sebastian-stumpf/abomination/pcb/sepp/models/xiao_rp2040.step

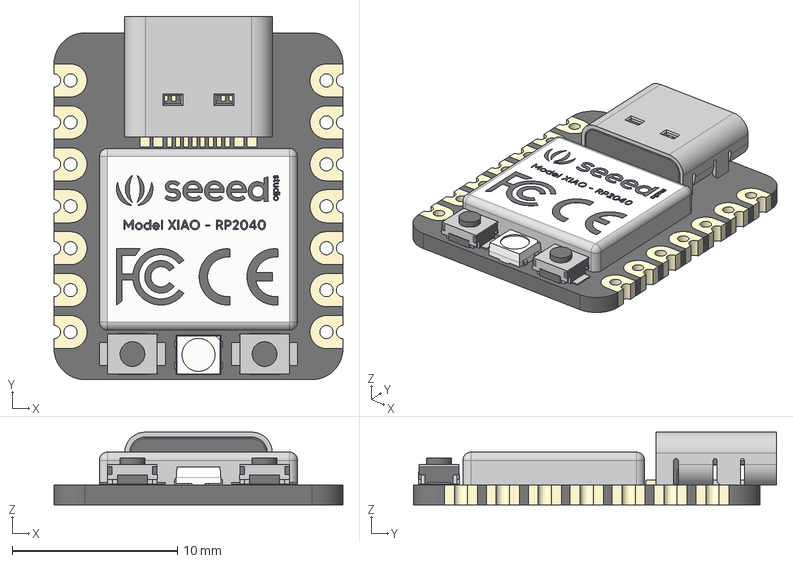
[picture p17: CAD file, 2023-10-14]
pcb/sepp/models/xiao_rp2040.step
17.5 x 22.0 x 4.40 mm
type-c v2
smd_button v3
DOUT
DIN
VSS
VDD
smd_button v3(Mirror)
