sebastian-stumpf/abomination/pcb/sepp/models/Liatris.step

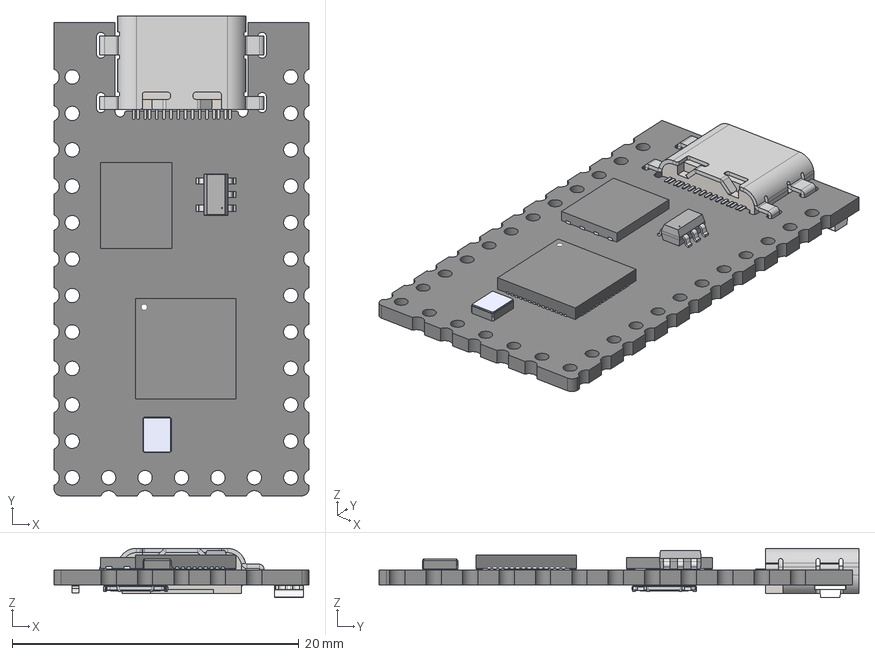
[picture p18: CAD file, 2023-10-14]
pcb/sepp/models/Liatris.step
17.8 x 33.5 x 3.44 mm
RP2040 PCB
