sebastian-stumpf/abomination/pcb/sepp/models/MBK-1u.step

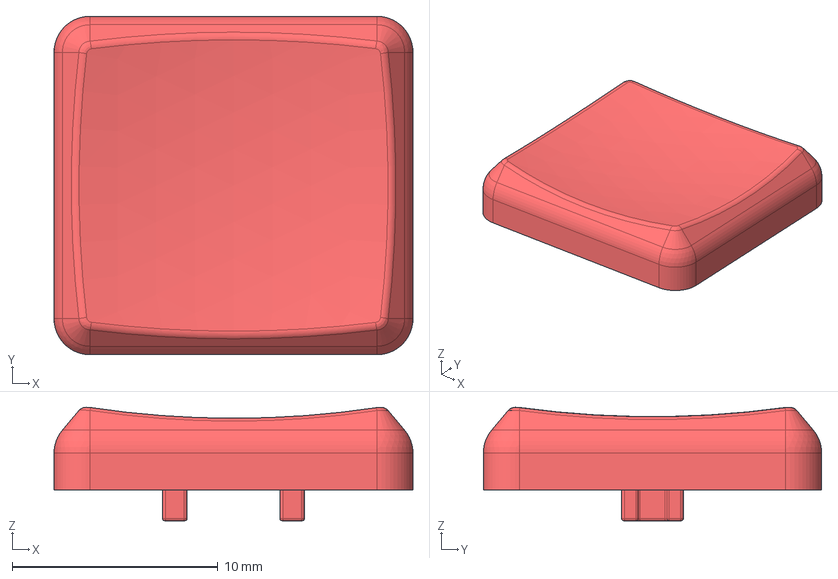
[picture p19: CAD file, 2023-10-14]
pcb/sepp/models/MBK-1u.step
17.4 x 16.4 x 5.52 mm
