sebastian-stumpf/abomination/pcb/sepp/models/pg1350-mbk.step

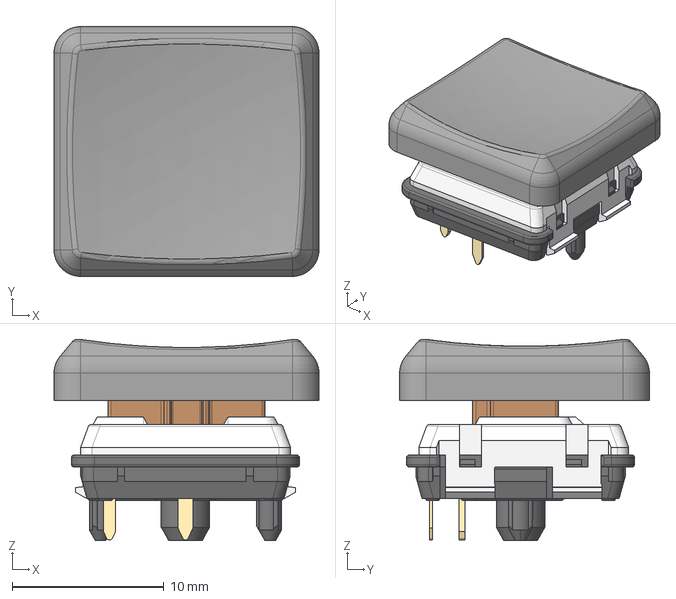
[picture p21: CAD file, 2023-10-14]
pcb/sepp/models/pg1350-mbk.step
17.4 x 16.4 x 13.3 mm
(Unsaved)
Document x 5
