sebastian-stumpf/abomination/pcb/sepp/models/EC12E-085.step

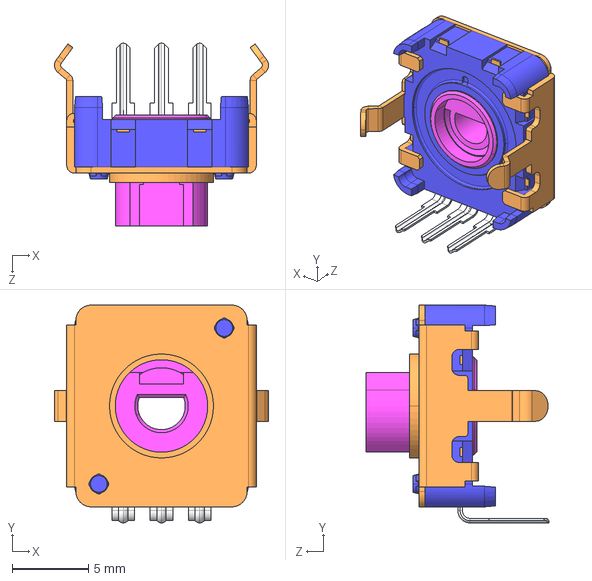
[picture p22: CAD file, 2023-10-14]
pcb/sepp/models/EC12E-085.step
14.0 x 14.3 x 11.9 mm
