sebastian-stumpf/abomination/pcb/sepp/models/SKRTLAE010.step

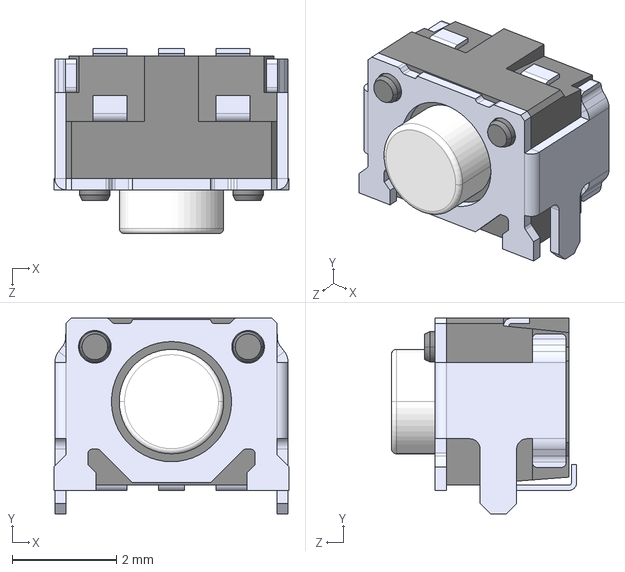
[picture p23: CAD file, 2023-10-14]
pcb/sepp/models/SKRTLAE010.step
4.50 x 3.75 x 3.55 mm
