sebastian-stumpf/abomination/pcb/sepp/models/SW_SKHLLC.step

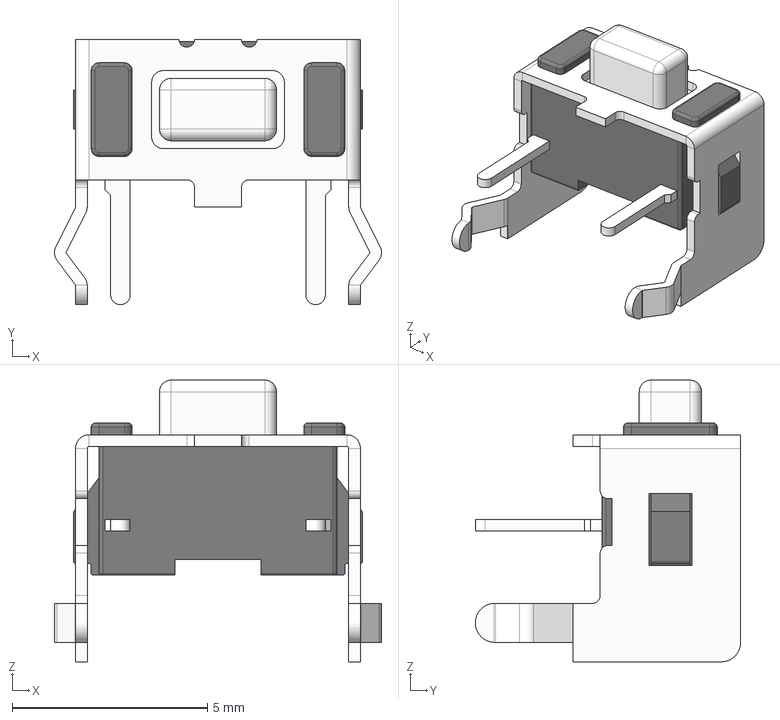
[picture p24: CAD file, 2023-10-14]
pcb/sepp/models/SW_SKHLLC.step
8.38 x 6.80 x 7.22 mm
