sebastian-stumpf/abomination/pcb/sepp/models/EC11-THT-15F-black.step

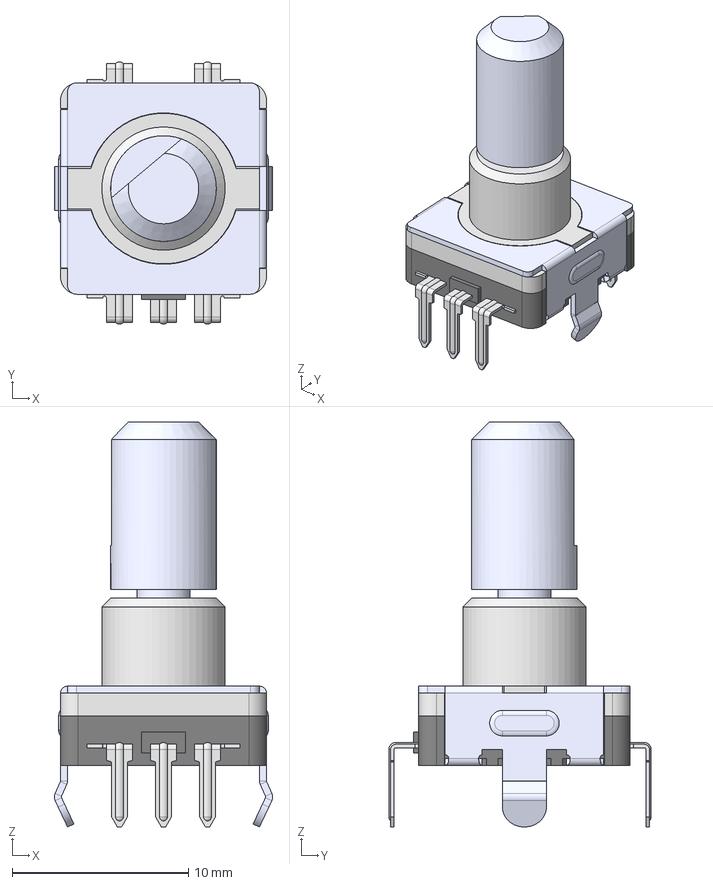
[picture p25: CAD file, 2023-10-14]
pcb/sepp/models/EC11-THT-15F-black.step
12.4 x 14.9 x 23.0 mm
Lb5
15F
EC11-Housing-THT
