sebastian-stumpf/abomination/pcb/sepp/models/LED_SK6812MINI-E.step

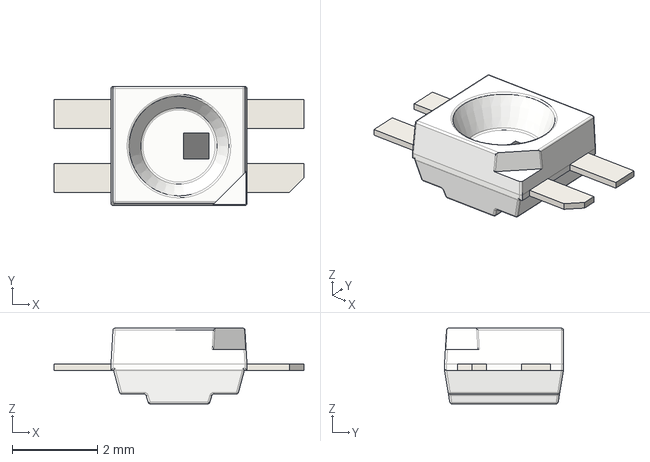
[picture p26: CAD file, 2023-10-14]
pcb/sepp/models/LED_SK6812MINI-E.step
5.88 x 2.80 x 1.78 mm
