sebastian-stumpf/abomination/pcb/sepp/models/SW_PUSH_6mm.step

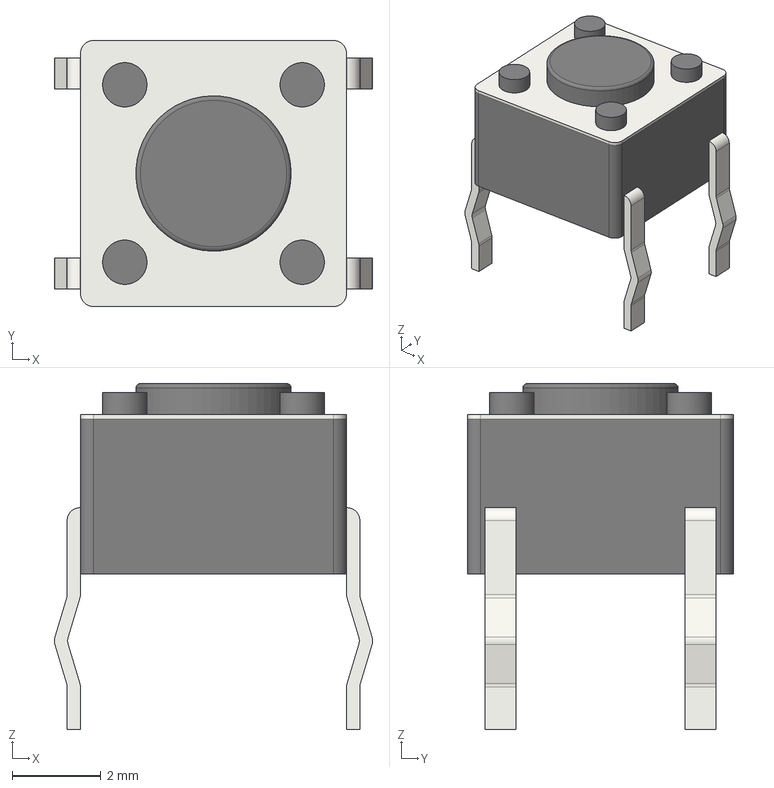
[picture p27: CAD file, 2023-10-14]
pcb/sepp/models/SW_PUSH_6mm.step
7.17 x 6.00 x 7.80 mm
