sebastian-stumpf/abomination/pcb/sepp/models/cherry mx.STEP

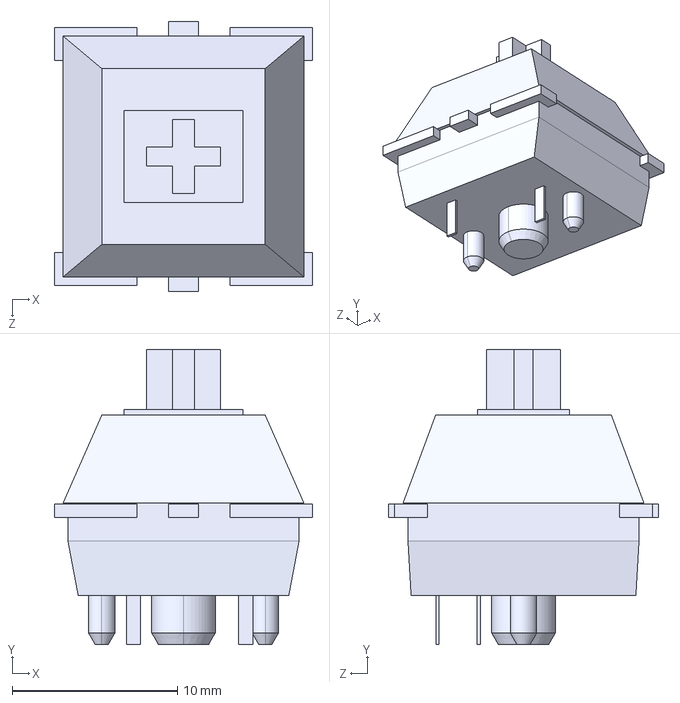
[picture p28: CAD file, 2023-10-14]
pcb/sepp/models/cherry mx.STEP
15.6 x 17.9 x 16.3 mm
