sebastian-stumpf/abomination/pcb/sepp/models/abomination-trackpad-holder.step

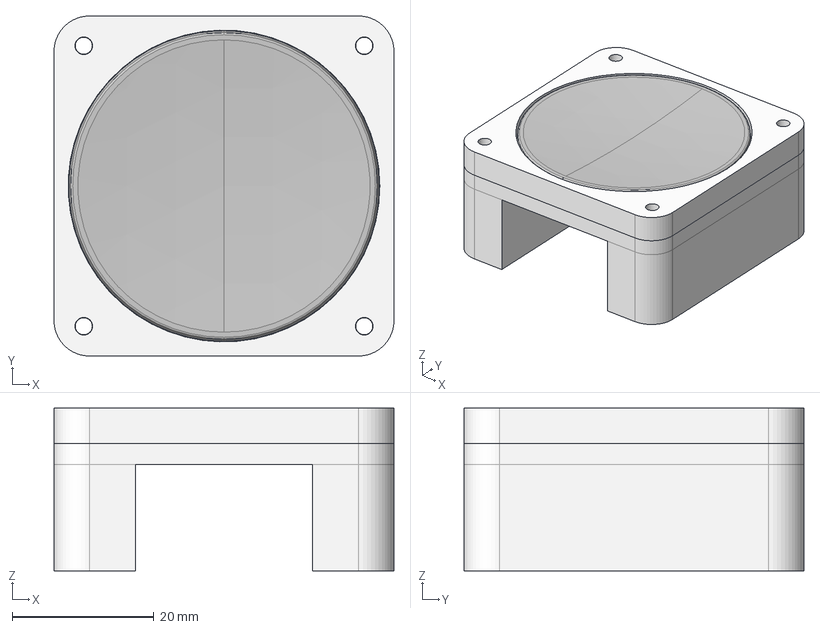
[picture p30: CAD file, 2023-10-14]
pcb/sepp/models/abomination-trackpad-holder.step
48.0 x 48.0 x 23.0 mm
trackpad
top
bottom
